mlab-modules/BATDATSOCKET01/doc/gen/dxf/BATDATSOCKET01-User_Eco1.dxf

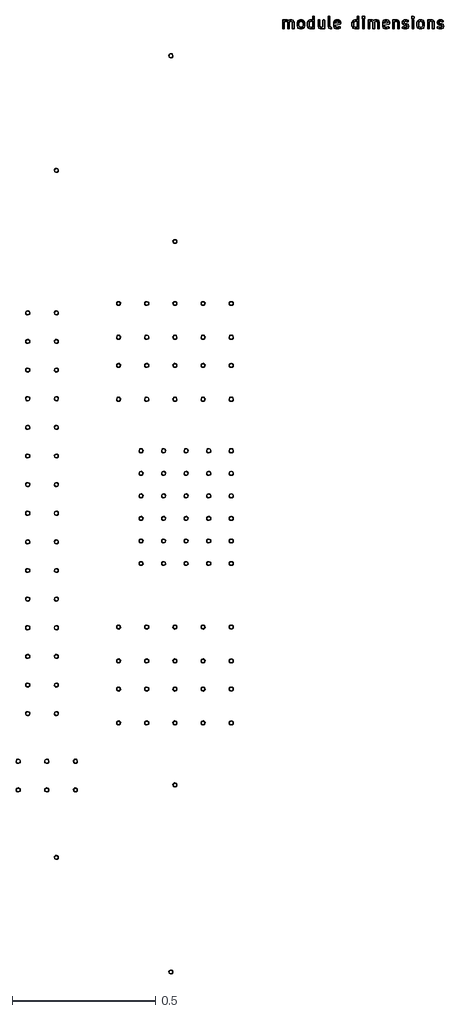
[picture p12: CAD file, 2025-05-14]
doc/gen/dxf/BATDATSOCKET01-User_Eco1.dxf
1.49 x 3.35
