mlab-modules/BATDATSOCKET01/doc/gen/dxf/BATDATSOCKET01-B_Cu.dxf

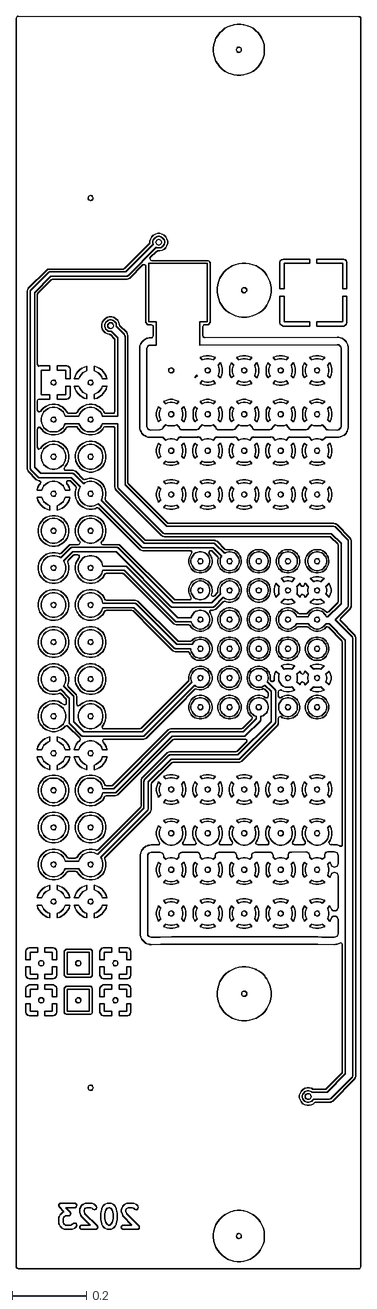
[picture p13: CAD file, 2025-05-14]
doc/gen/dxf/BATDATSOCKET01-B_Cu.dxf
0.929 x 3.38
